Coolbots7/openThermostat/src/openThermostat/Temperature.h

#ifndef TEMPERATURE_H
#define TEMPERATURE_H

double celsiusToFahrenheit(double celsius)
{
  return (celsius * 9 / 5) + 32;
}

double fahrenheitToCelsius(double fahrenheit)
{
  return (fahrenheit - 32) * 5 / 9;
}

#endif
